Gr3yR0n1n/BSidesSLC2015/Code/BSidesSLC2015/bitmaps.h

/*
    Filename: bitmaplibrary.h
    Purpose: Store your bitmaps in here :D
    Created: March 16, 2013
    Author: d3c4f

    NOTES: A bitmap converter can be downloaded at:
           http://en.radzio.dxp.pl/bitmap_converter/

    Special Thanks: Wade Smith for the Nyan Cat frames
*/

#ifndef BITMAPS_H
#define BITMAPS_H

// BSidesSLC Logo
const uint8_t BSidesSLC[] = {
    0x00, 0x00, 0x00, 0x00, 0x00, 0x00, 0x00, 0x00, 0x00, 0x00, 0x00, 0x00, 0x00, 0x00, 0x00, 0x00,
    0x00, 0x00, 0x00, 0x00, 0x00, 0x00, 0x00, 0x00, 0x00, 0x00, 0x00, 0x00, 0x00, 0x00, 0x00, 0x00,
    0x00, 0x00, 0x00, 0x00, 0x00, 0x00, 0x00, 0x00, 0x00, 0x00, 0x00, 0x00, 0x00, 0x00, 0x00, 0x00,
    0x00, 0x00, 0x00, 0x00, 0x00, 0xE0, 0xF0, 0xF0, 0xF0, 0xF0, 0xE0, 0x00, 0x00, 0x00, 0x00, 0x00,
    0x00, 0x00, 0x00, 0x00, 0x00, 0x00, 0x00, 0x00, 0x00, 0x00, 0x00, 0x00, 0x80, 0x80, 0x80, 0x00,
    0x00, 0x00, 0x00, 0x00, 0x00, 0x00, 0x00, 0xF0, 0xFF, 0xFF, 0xFF, 0x8F, 0x87, 0x87, 0xC7, 0xFF,
    0xFF, 0x7E, 0x3C, 0x00, 0x00, 0xC0, 0xF0, 0xF8, 0xFC, 0xFE, 0x7E, 0x3E, 0x1F, 0x1F, 0x1F, 0x1F,
    0x1F, 0x3E, 0x7E, 0xFC, 0xFC, 0xF8, 0xF0, 0xC0, 0x00, 0x00, 0x00, 0xE0, 0xF0, 0xF0, 0xF0, 0xFC,
    0xFF, 0xFC, 0xF0, 0xFE, 0xFE, 0xFE, 0xFE, 0xE0, 0xF8, 0xFF, 0xFF, 0xFF, 0xFF, 0xFF, 0xFF, 0xC0,
    0xF0, 0xF0, 0xF0, 0xF8, 0xF0, 0xF0, 0xFC, 0xFE, 0xFE, 0xFC, 0xF0, 0xF8, 0xF8, 0xE0, 0xF8, 0xF0,
    0xFF, 0xFF, 0xFF, 0xF0, 0xF0, 0x80, 0x00, 0x00, 0x00, 0x00, 0x7C, 0x7F, 0x7F, 0x7F, 0x71, 0x71,
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
    {0x3e, 0x41, 0x41, 0x41, 0x22}, // 43 C
    {0x7f, 0x41, 0x41, 0x22, 0x1c}, // 44 D
    {0x7f, 0x49, 0x49, 0x49, 0x41}, // 45 E
    {0x7f, 0x09, 0x09, 0x09, 0x01}, // 46 F
    {0x3e, 0x41, 0x49, 0x49, 0x7a}, // 47 G
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
    {0x78, 0x46, 0x41, 0x46, 0x78}  // 7f DEL
};

#endif
